KitB/therefore/hardware/case/biglid/case_main.scad

use <case.scad>

case(
part="main"
);
