KitB/therefore/hardware/case/biglid/lid.scad

use <case.scad>

case(
part="main"
);
