KitB/therefore/hardware/case/biglid/plate.scad

module plate() {
  difference(){
    import("../shapes/plate.svg");
    import("../shapes/buttons.svg");
  }
}

plate();
