KitB/therefore/hardware/case/screwless/printing/base.scad

use <../case.scad>;

base();
