KitB/therefore/hardware/case/screwless/printing/innards.scad

use <../case.scad>;

innards();
