KitB/therefore/firmware/python/therefore/layout.py

"""

Codes:
Special keys start with ':'

:t        transparent (get key from previous layer)
:_        no key here -- so this should never be accessed
:switch   switch between BLE and USB modes
:reset    reset the keyboard
:to(...)  go to layer '...' while button is held
:toggle(...) go to layer '...' until told otherwise

"""
# TODO: layout file should probably be called config (and contain more configuration than just layout?)
fn = ':to(functions)'
tfn = ':toggle(functions)'
gm = ':toggle(games)'
pp = 'playpause'
layout = {
    'layers': {
        'default': [
            ['`'    , '1', '2', '3', '4', '5', 'del'  , ':_',  ':_'     , ':switch'  , '6', '7', '8', '9', '0', '-'          ],
            ['tab'  , 'q', 'w', 'e', 'r', 't', '\\'   , ':_',  ':_'     , '['        , 'y', 'u', 'i', 'o', 'p', '='          ],
            ['esc'  , 'a', 's', 'd', 'f', 'g',  fn    , ':_',  ':_'     , ']'        , 'h', 'j', 'k', 'l', ';', '\''         ],
            ['shift', 'z', 'x', 'c', 'v', 'b', 'home' , 'ins', 'page_up', 'right_alt', 'n', 'm', ',', '.', '/', 'right_shift'],

            # `          1    2     3     4       5     d     s     6     7     8     9     0     -
            ['control', ' ', 'win', 'alt', 'spacebar', 'backspace', ':to(left thumb)', 'end', 'page_down', 'enter', 'spacebar', 'left', 'down', 'up', 'right', 'right_control'],
            [':_', ':_', ':_', ':_', ':_', ':_', ':_', 'win', 'win', ':_', ':_', ':_', ':_', ':_', ':_', 'konami'],
        ],
        'left thumb': [
            # `     1     2     3     4     5     d                 s     6     7     8     9     0     -
            [':t', ':t', ':t', ':t', ':t', ':t', ':t',      ':t', ':t', ':t', '^' , '&' , '*' , ':t', ':t', ':t'],
            [':t', ':t', ':t', ':t', ':t', ':t', ':switch',      ':t', ':t', ':t', ':t', ':t', ':t', ':t', ':t', ':t'],
            [':t', pp  , ':t', '-' , '_' , ':t',  tfn, ':t', ':t', ':t', ':t', '(' , ')' , '#' , '~' , ':t'],
            [':t', ':t', ':t', ':t', ':t', ':t', ':t',      ':t', ':t', ':t', ':t', '[' , ']' , ':t', ':t', ':t'],

            [':t', ':t', ':t', ':t', ':t', ':t', ':t',      ':t', ':t', ':t' , '_', 'prev_track', 'softer', 'louder', 'next_track', ':t'],
            [':t', ':t', ':t', ':t', ':t', ':t', ':t',      ':t', ':t', ':t', ':t', ':t' , ':t', ':t', ':t', ':t'],
        ],
        'functions': [
            # `     1     2     3     4     5                 d     s     6     7     8     9     0     -
            ['f11','f1', 'f2', 'f3', 'f4', 'f5', ':t', ':t', ':t', ':t', 'f6', 'f7', 'f8', 'f9', 'f10','f12'],
            [':t', ':t', ':t', ':t', ':t', ':t', ':t', ':t', ':t', ':t', ':t', ':t', ':t', ':t', ':t', ':t'],
            [':t', ':t', ':t', ':t', ':t', ':t', ':t', ':t', ':t', ':t', ':t', ':t', ':t', ':t', ':t', ':t'],
            [':t', ':t', ':t', ':t', ':t', ':t', ':t', ':t', ':t', ':t', ':t', ':t', ':t', ':t', ':t', ':t'],

            [':t', ':t', ':t', ':t', ':t', ':t', ':t', ':t', ':t', ':t', ':t', ':t', ':t', ':t', ':t', ':t'],
            [':t', ':t', ':t', ':t', ':t', ':t', ':t', ':t', ':t', ':t', ':t', ':t', ':t', ':t', ':t', ':t'],
        ],
        'games': [
            ['`'    , '1', '2', '3', '4', '5', 'del'  , ':_',  ':_'     , gm         , '6', '7', '8', '9', '0', '-'          ],
            ['tab'  , 'q', 'w', 'e', 'r', 't', '\\'   , ':_',  ':_'     , '['        , 'y', 'u', 'i', 'o', 'p', '='          ],
            ['esc'  , 'a', 's', 'd', 'f', 'g',  fn    , ':_',  ':_'     , ']'        , 'h', 'j', 'k', 'l', ';', '\''         ],
            ['shift', 'z', 'x', 'c', 'v', 'b', 'home' , 'ins', 'page_up', 'right_alt', 'n', 'm', ',', '.', '/', 'right_shift'],

            # `          1    2     3     4       5     d     s     6     7     8     9     0     -
            ['control', ' ', ' ', 'alt', 'spacebar', 'backspace', ':to(left thumb)', 'end', 'page_down', 'enter', 'spacebar', 'left', 'down', 'up', 'right', 'right_control'],
            [':_', ':_', ':_', ':_', ':_', ':_', ':_', 'win', 'win', ':_', ':_', ':_', ':_', ':_', ':_', ':_'],
        ],
    },
}
